GilboaCode/Gilboa_Water_Temp/KiCAD/Sender_Receiver.kicad_sch

## KiCad design KiCAD/Sender_Receiver.kicad_sch (2026-09-27)

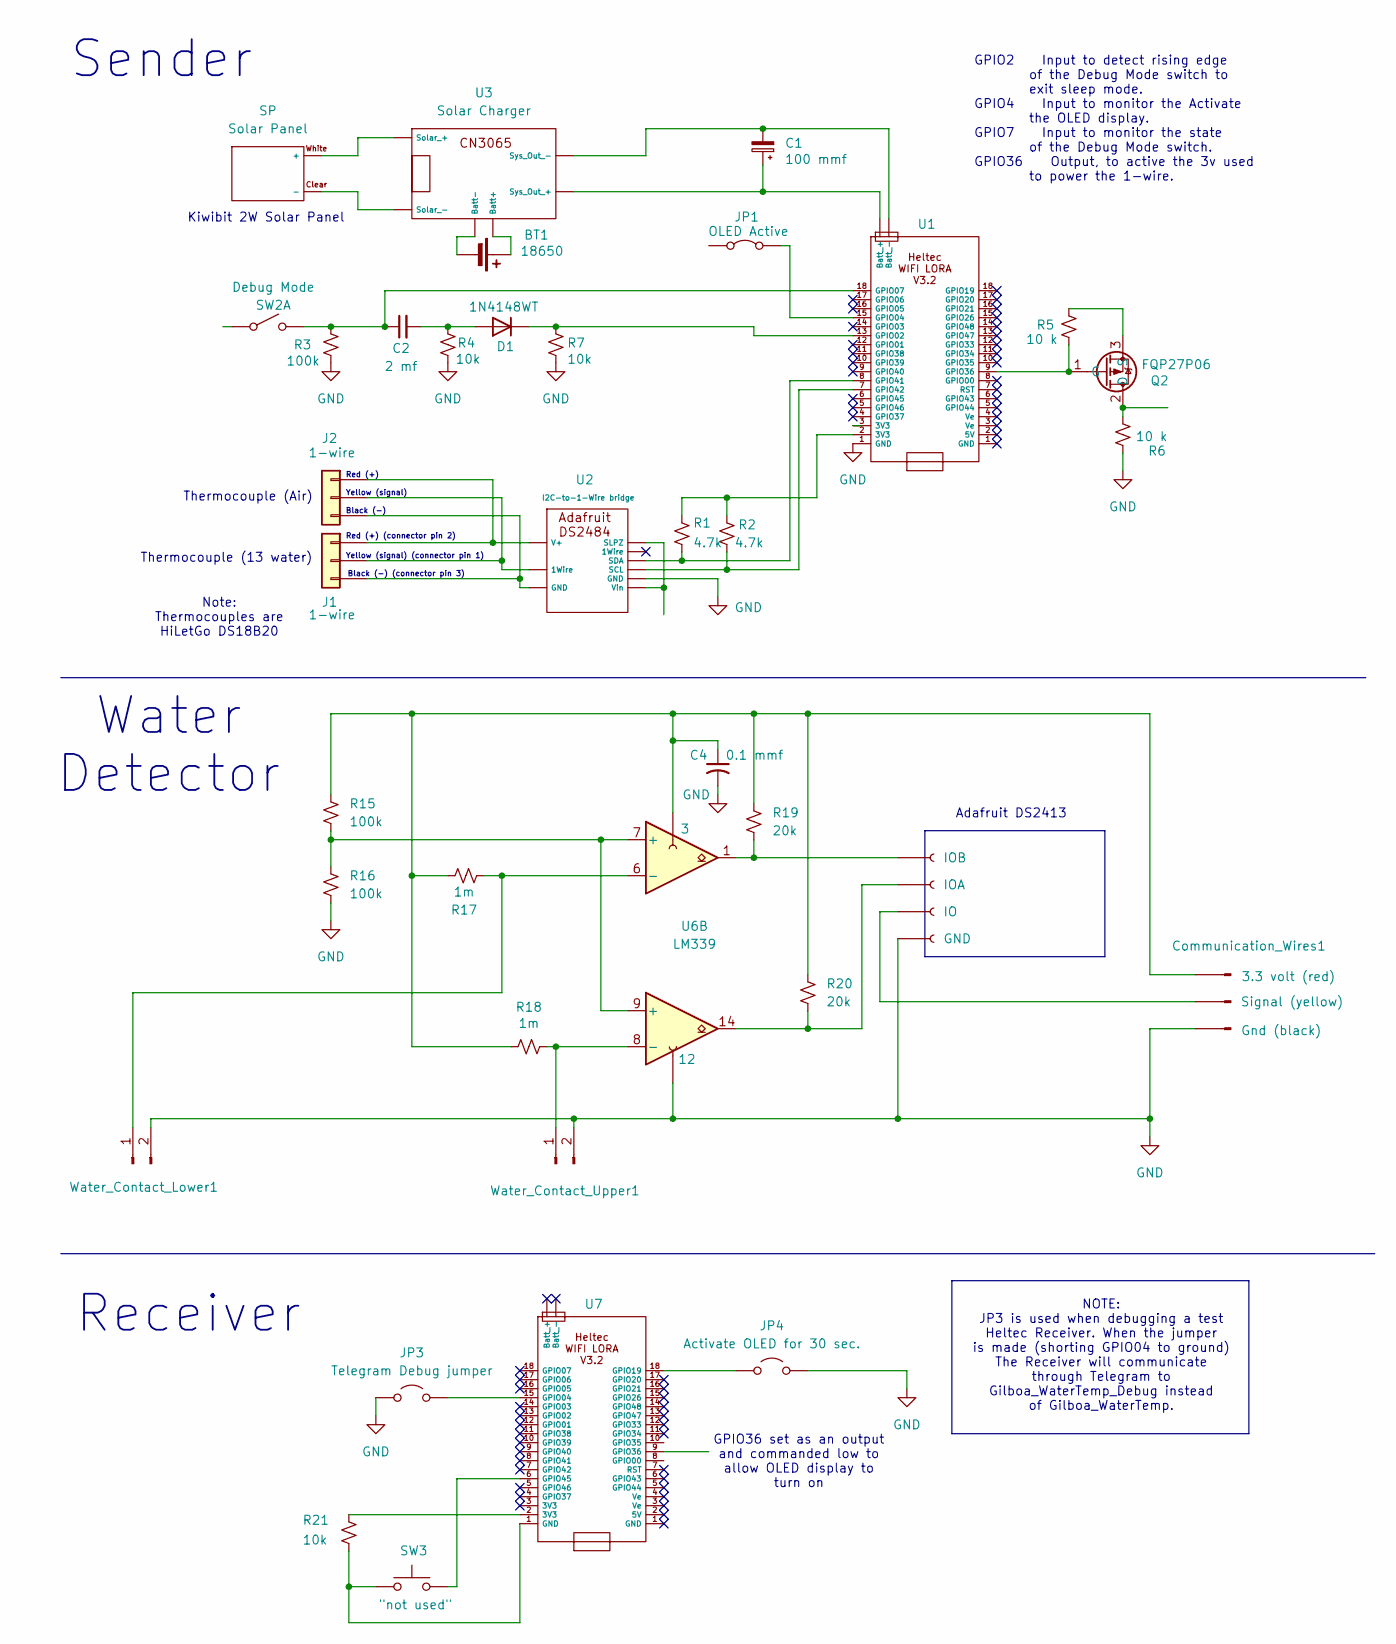
[picture p8: schematic Sender_Receiver.kicad_sch]

Parts:
BT1: 18650
C1: 100 mmf
C2: 2 mf
C4: 0.1 mmf
Communication_Wires1: 3.3 volt (red)
D1: 1N4148WT; D_SOD-523
J1, J2: 1-wire
J11: 3
J12: 12
J13: IOB
J14: IOA
J15: IO
J16: GND
J17: Signal (yellow)
J18: Gnd (black)
JP1: OLED Active
JP3: Telegram Debug jumper
JP4: Activate OLED for 30 sec.
Q2: FQP27P06; TO-220-3_Vertical
R1, R2: 4.7k
R3, R15, R16: 100k
R4, R7, R21: 10k
R5, R6: 10 k
R17, R18: 1m
R19, R20: 20k
SP: Solar Panel
SW2: Debug Mode
SW3: (no value)
U1, U7: (no value)
U2: I2C-to-1-Wire bridge
U3: Solar Charger
U6: LM339
Water_Contact_Lower1: (no value)
Water_Contact_Upper1: (no value)

Connections:
GND: C4.2, J12.1, J16.1, J18.1, JP3.1 (A), JP4.2 (B), R3.2, R4.2, R6.1, R7.2, R16.2, U1.1 (GND), U2., Water_Contact_Lower1.2, Water_Contact_Upper1.2
unnamed: BT1.1 (+), U3.
unnamed: BT1.2 (-), U3.
unnamed: C1.1, U1. (Batt_+), U3.
unnamed: C1.2, U1. (Batt_+), U3.
unnamed: C2.1, R3.1, SW2.2 (B), U1.18 (GPIO07)
unnamed: C2.2, D1.2 (A), R4.1
unnamed: C4.1, Communication_Wires1.1, J11.1, R15.1, R17.1, R18.1, R19.2, R20.2
unnamed: D1.1 (K), R7.1, U1.13 (GPIO02)
unnamed: J1.1, J2.1, U2.
unnamed: J1.2, J2.2, U2.
unnamed: J1.3, J2.3, U2.
unnamed: J13.1, R19.1, U6.1
unnamed: J14.1, R20.1, U6.14
unnamed: J15.1, J17.1
unnamed: JP1.2 (B), U1.15 (GPIO04)
unnamed: JP3.2 (B), U7.15 (GPIO04)
unnamed: JP4.1 (A), U7.18 (GPIO07)
unnamed: Q2.1 (G), R5.1, U1.9 (GPIO40)
unnamed: Q2.2 (D), R6.2
unnamed: Q2.3 (S), R5.2
unnamed: R1.1, R2.1, U1.2 (3V3)
unnamed: R1.2, U1.8 (GPIO41), U2.
unnamed: R2.2, U1.7 (GPIO42), U2.
unnamed: R15.2, R16.1, U6.7 (+), U6.9 (+)
unnamed: R17.2, U6.6 (-), Water_Contact_Lower1.1
unnamed: R18.2, U6.8 (-), Water_Contact_Upper1.1
unnamed: R21.1, U7.2 (3V3)
unnamed: R21.2, SW3.1 (A), SW3.2 (A), U7.1 (GND)
unnamed: SP., U3.
unnamed: SW3.3 (B), SW3.4 (B), U7.6 (GPIO45)

Notes on the sheet:
Red (+)
GPIO2 Input to detect rising edge of the Debug Mode switch to exit sleep mode. GPIO4 Input to monitor the Activate the OLED display. GPIO7 Input to monitor the state of the Debug Mode switch. GPIO36 Output, to active the 3v used to power the 1-wire.
Sender
Receiver
Red (+) (connector pin 2)
GPIO36 set as an output and commanded low to allow OLED display to turn on
Kiwibit 2W Solar Panel
Black (-)
Water Detector
Black (-) (connector pin 3)
Note: Thermocouples are HiLetGo DS18B20
Adafruit DS2413
Yellow (signal) (connector pin 1)
NOTE: JP3 is used when debugging a test Heltec Receiver. When the jumper is made (shorting GPIO04 to ground) The Receiver will communicate through Telegram to Gilboa_WaterTemp_Debug instead of Gilboa_WaterTemp.
Thermocouple (Air)
Thermocouple (13 water)
Yellow (signal)
